simoninns/TMS6100-Emulator/Firmware/tms6100/romdata_us.h

/************************************************************************
	romdata_us.h

    TI American TMS6100 PHROMA image
    Copyright (C) 2018 Simon Inns

    This file is part of the TMS6100-Emulator.

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
    Email: simon.inns@gmail.com

************************************************************************/

#ifndef ROMDATA_US_H_
#define ROMDATA_US_H_

// Define the PHROM number 0-15 (defines the 16K address space that the PHROM
// should respond to.
//
// Note: On the BBC Micro the SOUND command uses -16 (0xFFF0) for the US PHROM,
// meaning the PHROM BANK number is 0
#define PHROM_BANK 0x0

// Note: This is a dump of the TI American Speech PHROM produced using HxD
// and contains 16K bytes of data (16,384 bytes or 0x4000 in hex).

/*
	PHROM Word list:
	
	Word or   Absolute
	word-part address
	number    (hex)    Word
	
	1         019E     ZERO
	2         01EB     FOUR
	3         0237     EIGHT
	4         026A     TWELVE
	5         02B3     TWENTY
	6         02FF     ONE
	7         0342     FIVE
	8         0395     NINE
	9         03ED     THIR-
	10        0425     HUNDRED
	11        047C     TWO
	12        04B3     SIX
	13        04E5     TEN
	14        051B     FIF-
	15        0541     THOUSAND
	16        05BA     THREE
	17        0606     SEVEN
	18        0650     ELEVEN
	19        06B8     TEEN-
	20        06EE     B
	21        0720     F
	22        075A     J
	23        079D     N
	24        07DD     R
	25        0809     V
	26        085D     ZEE
	27        0899     C
	28        08DB     G
	29        0919     K
	30        095A     O
	31        0988     S
	32        09B8     W
	33        0A1E     D
	34        0A52     H
	35        0A8D     L
	36        0ACC     P
	37        0B02     T
	38        0B3C     X
	39        0B75     A
	40        0BA3     E
	41        0BD9     I
	42        0C1B     M
	43        0C5A     Q
	44        0C8E     U
	45        0CCC     Y
	46        0D0E     ALPHA
	47        0D4F     ECHO
	48        0D91     DELTA
	49        0DE4     BRAVO
	50        0E41     FOXTROT
	51        0EB0     CHARLIE
	52        0F01     GOLF
	53        0F39     HENRY
	54        0F89     LIMA
	55        0FD2     PAPA
	56        1014     TANGO
	57        106C     XRAY
	58        10D0     THE
	59        10F7     WATTS
	60        1146     METER
	61        1191     DANGER
	62        11E4     PRESSURE
	63        1228     CHANGE
	64        1291     MINUS
	65        12E1     NOT
	66        1326     START
	67        1371     LINE
	68        13C5     OFF
	69        13F1     TIME
	70        142E     AUTOMATIC
	71        14AC     WEIGHT
	72        14FB     SMOKE
	73        153C     ABORT
	74        15A6     CALL
	75        15E2     CYCLE
	76        1630     DISPLAY
	77        168B     EQUAL
	78        16DD     FAST
	79        172B     ABOUT
	80        1788     GO
	81        17AE     INCH
	82        17F4     LOW
	83        1824     MOTOR
	84        1869     OPEN
	85        18B2     PERCENT
	86        1904     PROBE
	87        194E     READY
	88        198E     SET
	89        19CC     SPEED
	90        1A16     UNDER
	91        1A6A     OPERATOR
	92        1AE7     INDIA
	93        1B3B     MIKE
	94        1B7D     QUEBEC
	95        1BC4     UNIFORM
	96        1C42     YANKEE
	97        1CA5     AMPS
	98        1CE0     MEGA
	99        1D2A     PICO
	100       1D80     FIRE
	101       1DD3     POWER
	102       1E21     COMPLETE
	103       1E8B     REPAIR
	104       1EEC     TEMPERATURE
	105       1F41     STOP
	106       1F70     MACHINE
	107       1FCE     ON
	108       200A     CONTROL
	109       2071     ELECTRICIAN
	110       20E2     AT
	111       2111     RED
	112       2160     ALL
	113       2197     CANCEL
	114       21DD     PHASE
	115       221F     NOR
	116       226C     EXIT
	117       22BA     FLOW
	118       22FB     GAUGE
	119       234A     GREEN
	120       23B9     INSPECTOR
	121       242A     MANUAL
	122       24A1     MOVE
	123       24FC     OVER
	124       2547     PLUS
	125       2583     PULL
	126       25BD     REPEAT
	127       2621     SHUT
	128       2658     TEST
	129       2696     VOLTS
	130       26D3     GALLONS
	131       2737     JULIET
	132       279D     NOVEMBER
	133       2814     ROMEO
	134       2874     VICTOR
	135       28CB     ZULU
	136       2914     HERTZ
	137       2948     MICRO
	138       299C     OHMS
	139       29F0     AREA
	140       2A43     CIRCUIT
	141       2A9E     CONNECT
	142       2AEB     SECONDS
	143       2B55     UNIT
	144       2BB2     TIMER
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
	0xF2, 0x3D, 0x48, 0x3E, 0x8B, 0x3E, 0x69, 0xFB, 0x59, 0xDD, 0x51, 0xD5,
	0xD7, 0xB5, 0x6F, 0x0A, 0x78, 0xC0, 0x52, 0x01, 0x0F, 0x50, 0xAC, 0xF6,
	0xA8, 0x16, 0x15, 0xF2, 0x7B, 0xEA, 0x19, 0x47, 0xD0, 0x64, 0xEB, 0xAD,
	0x76, 0xB5, 0xEB, 0xD1, 0x96, 0x24, 0x6E, 0x62, 0x6D, 0x5B, 0x1F, 0x0A,
	0xA7, 0xB9, 0xC5, 0xAB, 0xFD, 0x1A, 0x62, 0xF0, 0xF0, 0xE2, 0x6C, 0x73,
	0x1C, 0x73, 0x52, 0x1D, 0x19, 0x94, 0x6F, 0xCE, 0x7D, 0xED, 0x6B, 0xD9,
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
};

#endif /* ROMDATA_US_H_ */
